MOAalpha/2526_Maker_EscapeGame/LIVRABLES/Batterie2S1P.jpeg

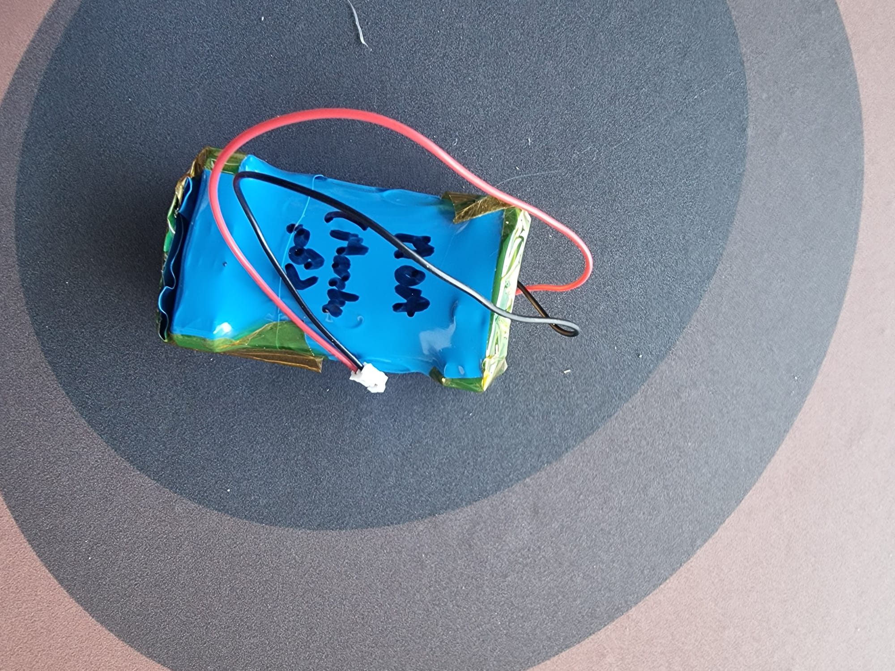
LIVRABLES/Batterie2S1P.jpeg
