MOAalpha/2526_Maker_EscapeGame/LIVRABLES/Couture-Extérieur.jpeg

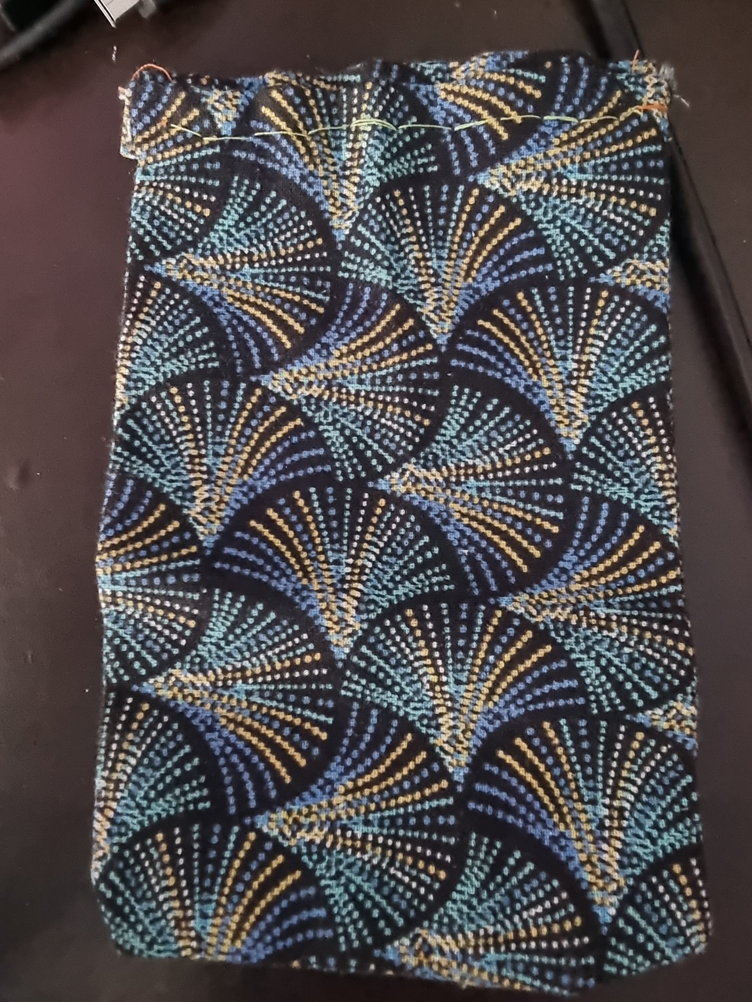
LIVRABLES/Couture-Extérieur.jpeg
