MOAalpha/2526_Maker_EscapeGame/LIVRABLES/Impression3D-Face1.jpeg

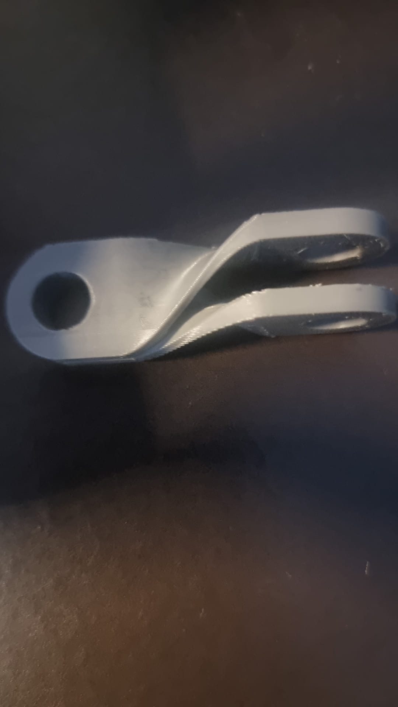
LIVRABLES/Impression3D-Face1.jpeg
