MOAalpha/2526_Maker_EscapeGame/MAKER/Code/TestEcran/TestEcran_Nucleo/Core/Inc/main.h

#define B1_Pin GPIO_PIN_13
#define B1_GPIO_Port GPIOC
#define B1_EXTI_IRQn EXTI15_10_IRQn
#define USART_TX_Pin GPIO_PIN_2
#define USART_TX_GPIO_Port GPIOA
#define USART_RX_Pin GPIO_PIN_3
#define USART_RX_GPIO_Port GPIOA
#define LD2_Pin GPIO_PIN_5
#define LD2_GPIO_Port GPIOA
#define LCD_RES_Pin GPIO_PIN_7
#define LCD_RES_GPIO_Port GPIOC
#define LCD_DC_Pin GPIO_PIN_9
#define LCD_DC_GPIO_Port GPIOA
#define TMS_Pin GPIO_PIN_13
#define TMS_GPIO_Port GPIOA
#define TCK_Pin GPIO_PIN_14
#define TCK_GPIO_Port GPIOA
#define TTP_1_Pin GPIO_PIN_15
#define TTP_1_GPIO_Port GPIOA
#define TTP_1_EXTI_IRQn EXTI15_10_IRQn
#define SWO_Pin GPIO_PIN_3
#define SWO_GPIO_Port GPIOB
#define LCD_CS_Pin GPIO_PIN_6
#define LCD_CS_GPIO_Port GPIOB
#define TTP_0_Pin GPIO_PIN_8
#define TTP_0_GPIO_Port GPIOB
#define TTP_0_EXTI_IRQn EXTI9_5_IRQn
