MOAalpha/2526_Maker_EscapeGame/MAKER/Code/TestEcran/TestEcran_Nucleo/Core/Inc/myutils.h

/*
 * myutils.h
 *
 *  Created on: 13 avr. 2026
 *      Author: mathe
 */

#ifndef INC_MYUTILS_H_
#define INC_MYUTILS_H_

void start_story();
void bad_end_story();
void good_end_story();
void damier();


#endif /* INC_MYUTILS_H_ */
